unit-cell/toes/Software/config.h

// change these values to set custom MIDI messages.

int midi_out_channel = 14; // MIDI OUT channel

int note1 = 61; // foot switch 1 MIDI note
int note2 = 62; // foot switch 2 MIDI note
int note3 = 68; // foot switch 3 MIDI note
int note4 = 69; // foot switch 4 MIDI note

int note_sus = 61; // sustain pedal MIDI note
int midi_cc = 43; // MIDI CC message for expression pedal
